jgillick/ThunderPack/examples/libopencm3/RunningLEDs/README.md

# Running LEDs

Make all the LEDs "run" by turning them on in order, and then off again.
