jgillick/ThunderPack/examples/STM32Cube/Button/README.md

# Button Example

Simply turns on the LED when the button is pressed.

## Compiling/Flashing
See the instructions [here](../README.md)
