jgillick/ThunderPack/examples/ChibiOS/Blink2/README.md

# Blink - Non Blocking

This builds on the Blink program by using [virtual timers](http://www.chibios.org/dokuwiki/doku.php?id=chibios:book:kernel_vt) to insert the blink delay without pausing the execution of the reset of the program.

## Compiling/Flashing
See the instructions [here](../README.md)
