jgillick/ThunderPack/examples/STM32Cube/Blink/README.md

# Blink

The ubiquitous "Hello World" of hardware examples. This simply blinks the first LED (PA0). Pressing the button will blink the LED faster.

## Compiling/Flashing
See the instructions [here](../README.md)
