jgillick/ThunderPack/examples/STM32Cube/Fade/README.md

# Fade

Uses PWM to fade LED 1 (PA0) on and off.

## Compiling/Flashing
See the instructions [here](../README.md)
