jgillick/ThunderPack/examples/libopencm3/Fade/README.md

# Fade

Fade the first LED on and off

## Compiling/Flashing
See the instructions [here](../README.md)
