jgillick/ThunderPack/examples/libopencm3/Blink/README.md

# Blink

The ubiquitous "Hello World" of hardware examples. This simply blinks LED 1 (PA0). Pressing the button will blink the LED faster.

## Compiling/Flashing
See the instructions [here](../README.md)
