jgillick/ThunderPack/hardware/Original/pinout/pinout.jpg

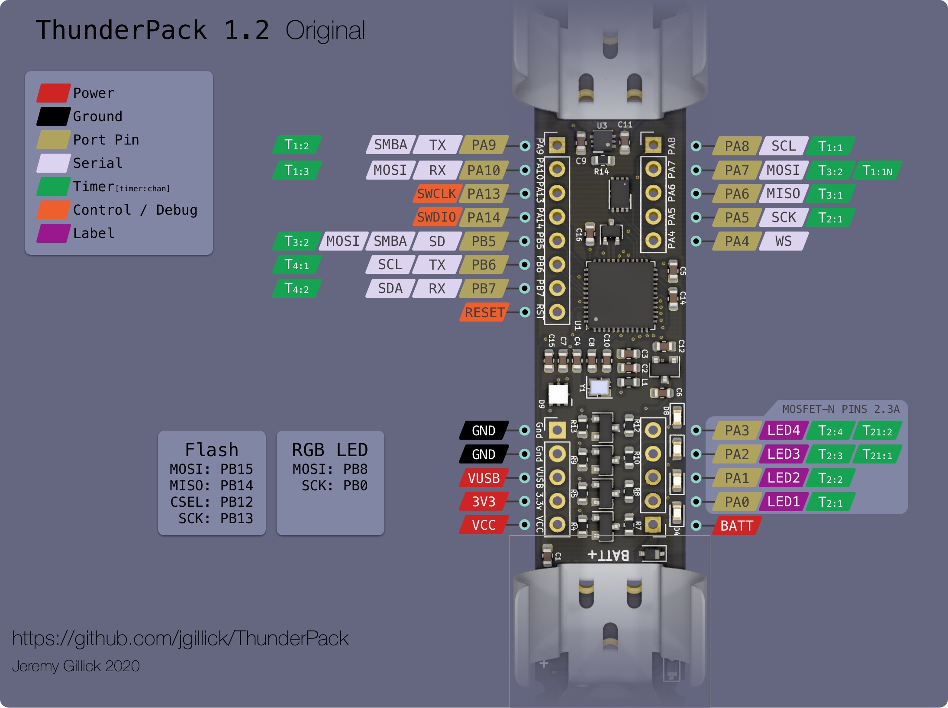
hardware/Original/pinout/pinout.jpg
