jgillick/ThunderPack/images/above.jpg

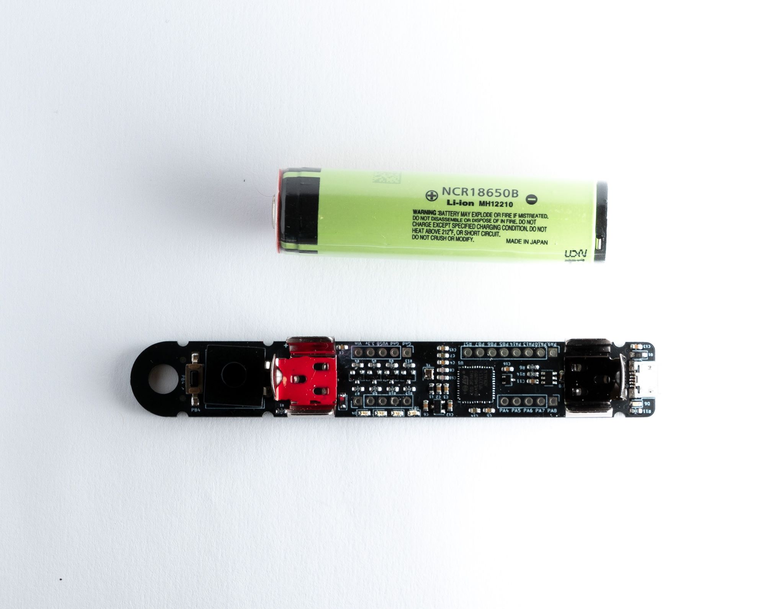
images/above.jpg
