jgillick/ThunderPack/images/animation.gif

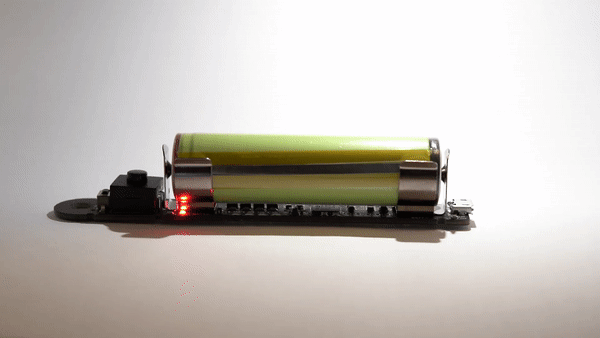
images/animation.gif
