jgillick/ThunderPack/images/battery.jpg

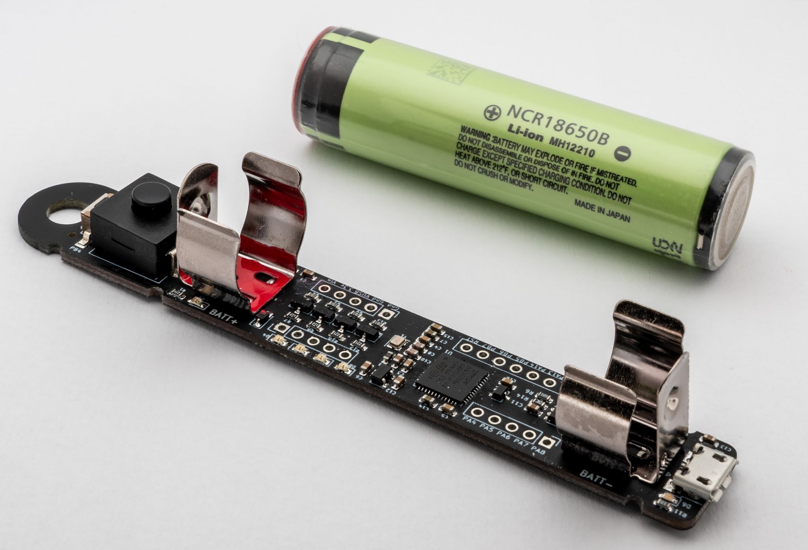
images/battery.jpg
