jgillick/ThunderPack/images/bootloader-mode.jpg

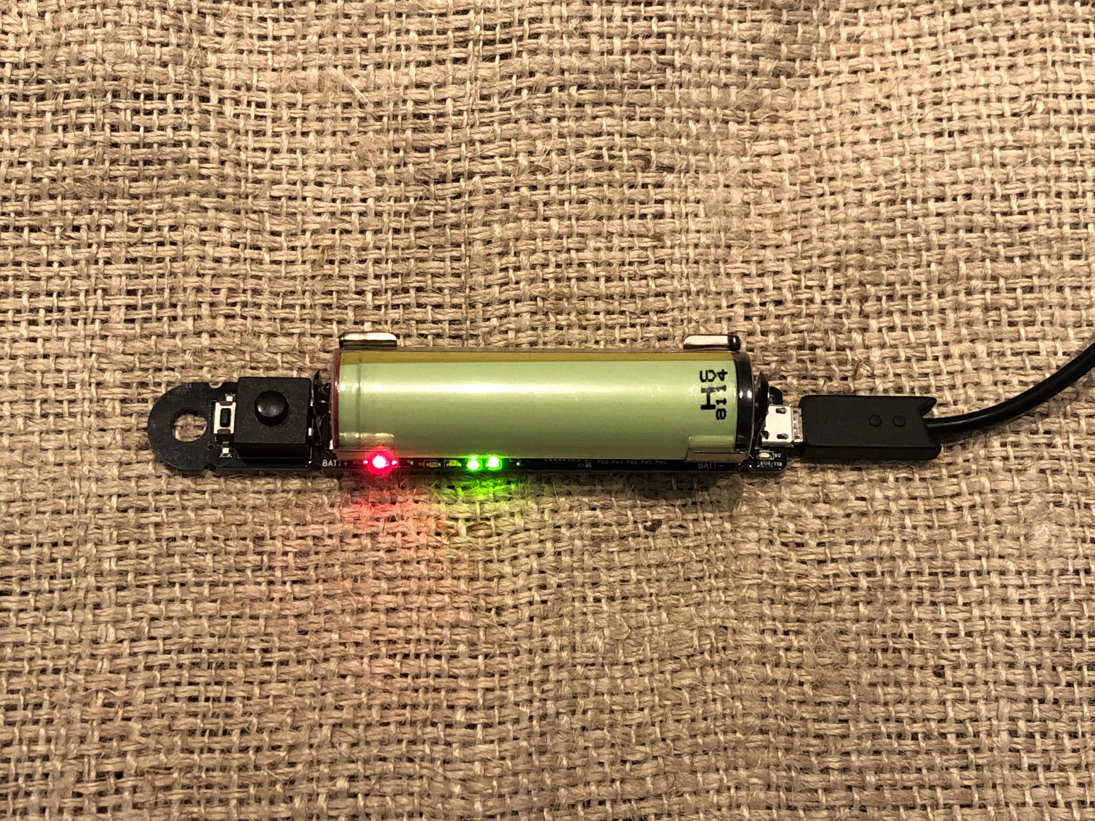
images/bootloader-mode.jpg
