jgillick/ThunderPack/images/breadboard_proto.jpg

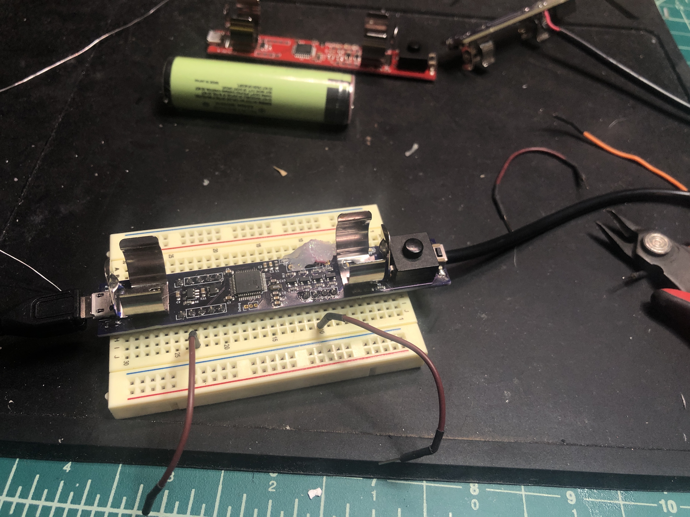
images/breadboard_proto.jpg
