jgillick/ThunderPack/images/compact/leds.gif

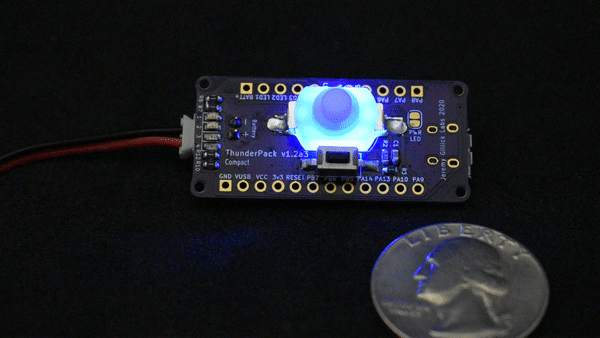
images/compact/leds.gif
