jgillick/ThunderPack/images/product/thunderpack.webp

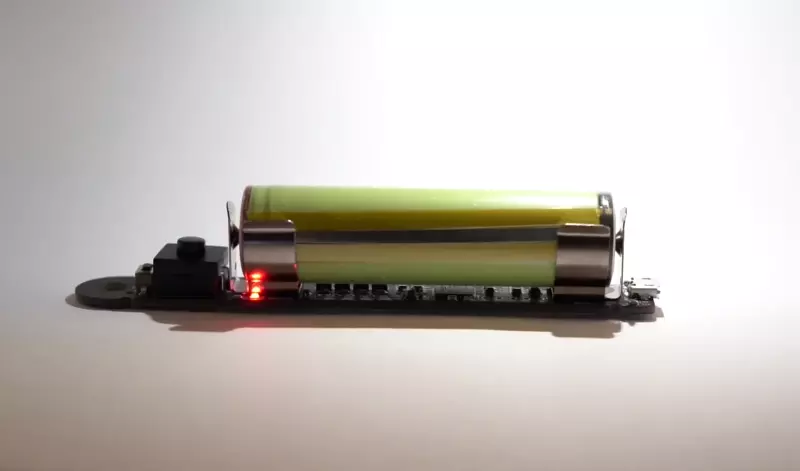
images/product/thunderpack.webp
