jgillick/ThunderPack/images/rev-pArm.jpg

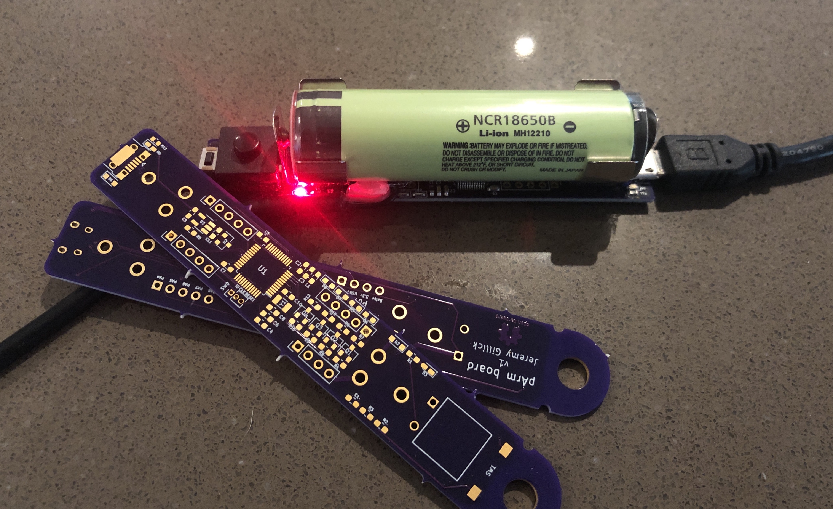
images/rev-pArm.jpg
