jgillick/ThunderPack/images/side.jpg

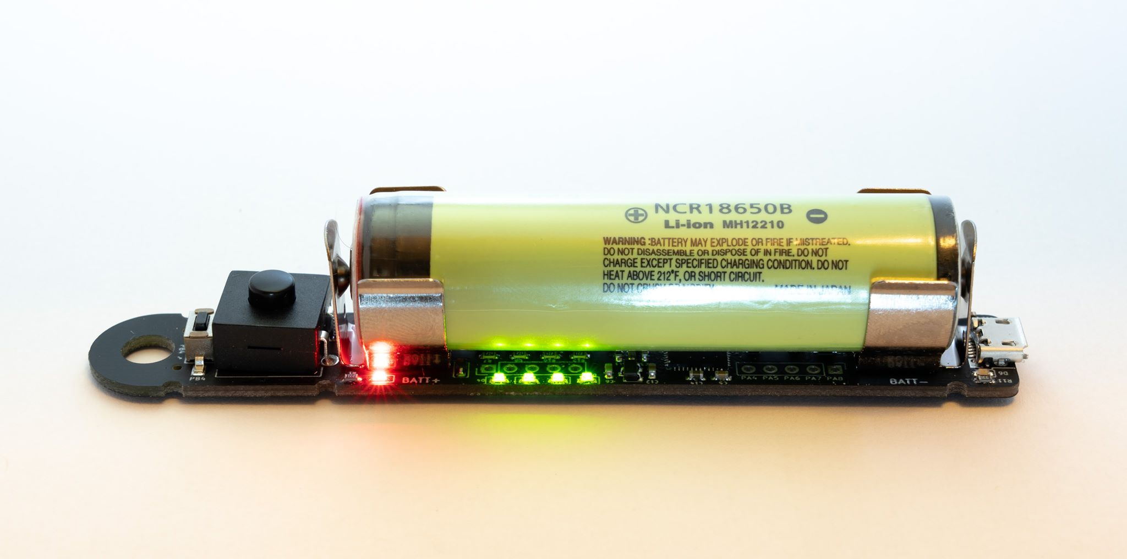
images/side.jpg
