jgillick/ThunderPack/examples/STM32Cube/USBSerial/Inc/main.h

/**
  ******************************************************************************
  * @file           : main.h
  * @brief          : Header for main.c file.
  *                   This file contains the common defines of the application.
  ******************************************************************************
  * @attention
  *
  * <h2><center>&copy; Copyright (c) 2020 STMicroelectronics.
  * All rights reserved.</center></h2>
  *
  * This software component is licensed by ST under Ultimate Liberty license
  * SLA0044, the "License"; You may not use this file except in compliance with
  * the License. You may obtain a copy of the License at:
  *                             www.st.com/SLA0044
  *
  ******************************************************************************
  */
#ifndef __MAIN_H
#define __MAIN_H

#include <stdint.h>

#ifdef __cplusplus
extern "C" {
#endif


/* Exported functions prototypes ---------------------------------------------*/
void Error_Handler(void);


#ifdef __cplusplus
}
#endif

#endif /* __MAIN_H */

/************************ (C) COPYRIGHT STMicroelectronics *****END OF FILE****/
